Shaurya-Ashu/waker/CAD/img_2.png

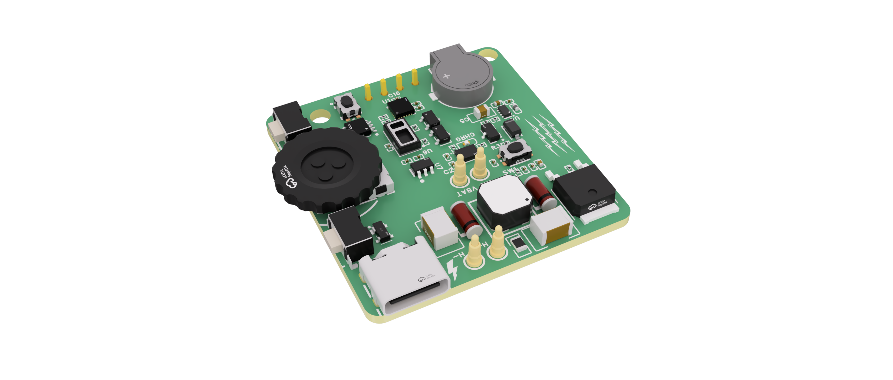
CAD/img_2.png
