Shaurya-Ashu/waker/CAD/IMG_3.png

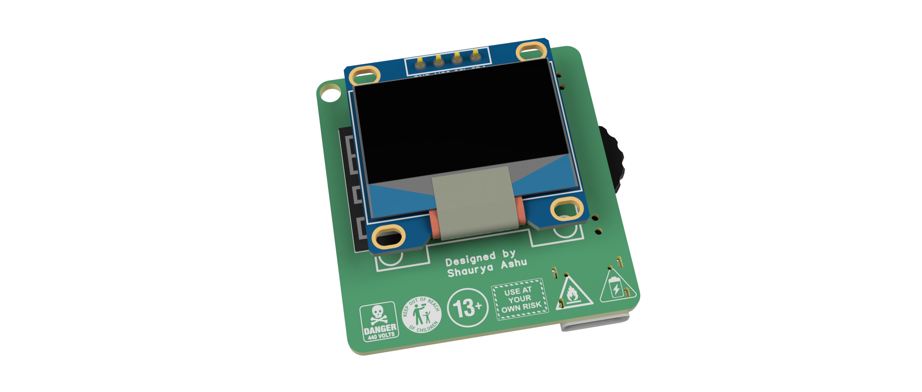
CAD/IMG_3.png
